emlyon/makers-beehive/img/roof/3.jpg

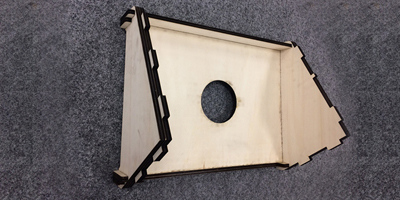
img/roof/3.jpg
